Sicatriz/ES2_GreenhouseProject/testCode/Humidity_Temp_HTS221.ino

/*
  HTS221 - Read Sensors + LPS22HB - Read Pressure

  This example reads data from the on-board HTS221 sensor of the
  Nano 33 BLE Sense and prints the temperature and humidity sensor
  values to the Serial Monitor once a second.

  This example also reads data from the on-board LPS22HB sensor of the Nano 33 BLE Sense, 
  converts the atmospheric pressure sensor values to altitude above sea level,
  and prints them to the Serial Monitor every second.

  additionaly this example reads audio data from the on-board PDM microphones, and prints
  out the samples to the Serial console. The Serial Plotter built into the
  Arduino IDE can be used to plot the audio data (Tools -> Serial Plotter)

  The circuit:
  - Arduino Nano 33 BLE Sense
*/

#include <Arduino_HTS221.h>
#include <Arduino_LPS22HB.h>
#include <PDM.h>
#include <LiquidCrystal.h>


float old_temp = 0;
float old_hum = 0;

// buffer to read samples into, each sample is 16-bits
short sampleBuffer[256];

// number of samples read
volatile int samplesRead;

// initialize the library by associating any needed LCD interface pin
// with the arduino pin number it is connected to
const int rs = 12, en = 11, d4 = 5, d5 = 4, d6 = 3, d7 = 2;
LiquidCrystal lcd(rs, en, d4, d5, d6, d7);

void setup() {
  Serial.begin(9600);
  while (!Serial);

  // check if HTS221 is found
  if (!HTS.begin()) {
    Serial.println("Failed to initialize humidity temperature sensor!");
    while (1);
  }

  // check if LPS22HB is found
  if (!BARO.begin()) {
    Serial.println("Failed to initialize pressure sensor!");
    while (1);
  }

  // microphone (PDM) setup
  // configure the data receive callback
  PDM.onReceive(onPDMdata);

  // optionally set the gain, defaults to 20
  // PDM.setGain(30);

  // initialize PDM with:
  // - one channel (mono mode)
  // - a 16 kHz sample rate
  if (!PDM.begin(1, 16000)) {
    Serial.println("Failed to start PDM!");
    while (1);
  }

  // set up the LCD's number of columns and rows:
  lcd.begin(16, 2);
  // Turn off the display:
  lcd.noDisplay();
  delay(500);
    // Print a message to the LCD.
  lcd.print("Booted...");
  // Turn on the display:
  lcd.display();
  delay(500);

}

void loop() {
  // read all the sensor values
  float temperature = HTS.readTemperature();
  float humidity    = HTS.readHumidity();
  float pressure = BARO.readPressure();
  
  
 
  float altitude = 44330 * ( 1 - pow(pressure/101.325, 1/5.255) );

  //value = analogRead(pin, value);

  // check if the range values in temperature are bigger than 0,5 ºC
  // and if the range values in humidity are bigger than 1%
  if (abs(old_temp - temperature) >= 0.5 || abs(old_hum - humidity) >= 1 )
  {
    old_temp = temperature;
    old_hum = humidity;
    // print each of the sensor values
    Serial.print("Temperature = ");
    Serial.print(temperature);
    Serial.println(" °C");
    Serial.print("Humidity    = ");
    Serial.print(humidity);
    Serial.println(" %");
    Serial.println();
  }

  // print each of the sensor values
  Serial.print("Temperature = ");
  Serial.print(temperature);
  Serial.println(" °C");

  Serial.print("Humidity    = ");
  Serial.print(humidity);
  Serial.println(" %");

  Serial.print("Altitude according to kPa is = ");
  Serial.print(altitude);
  Serial.println(" m");

  // print an empty line
  Serial.println();

  // wait 1 second to print again
  delay(2000);

  // wait for samples to be read
  if (samplesRead) {

    // print samples to the serial monitor or plotter
    for (int i = 0; i < samplesRead; i++) {

      //uncomment for serial print value
      // Serial.println(sampleBuffer[i]);
      
      
      // check if the sound value is higher than 500
      if (sampleBuffer[i]>=250){
        digitalWrite(LEDR,LOW);
        digitalWrite(LEDG,HIGH);
        digitalWrite(LEDB,HIGH);
      }
      // check if the sound value is higher than 250 and lower than 500
      if (sampleBuffer[i]>=250 && sampleBuffer[i] < 250){
        digitalWrite(LEDB,LOW);
        digitalWrite(LEDR,HIGH);
        digitalWrite(LEDG,HIGH);
      }
      //check if the sound value is higher than 0 and lower than 250
      if (sampleBuffer[i]>=0 && sampleBuffer[i] < 150){
        digitalWrite(LEDG,LOW);
        digitalWrite(LEDR,HIGH);
        digitalWrite(LEDB,HIGH);
      }
    }

    // clear the read count
    samplesRead = 0;
  }
}

void onPDMdata() {
  // query the number of bytes available
  int bytesAvailable = PDM.available();

  // read into the sample buffer
  PDM.read(sampleBuffer, bytesAvailable);

  // 16-bit, 2 bytes per sample
  samplesRead = bytesAvailable / 2;
}
